jmederos/esp32-r50-kbus/hardware/images/IMG_3665.JPG

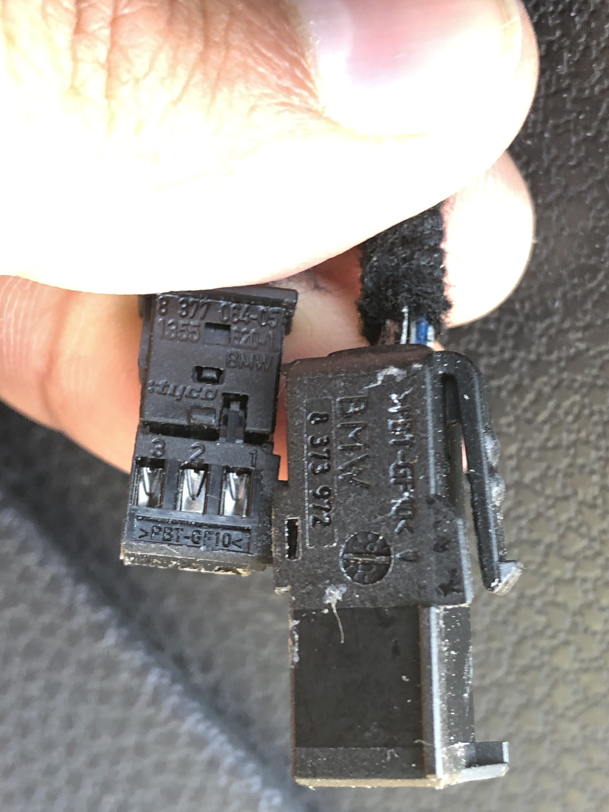
hardware/images/IMG_3665.JPG
