jmederos/esp32-r50-kbus/hardware/images/IMG_3666.JPG

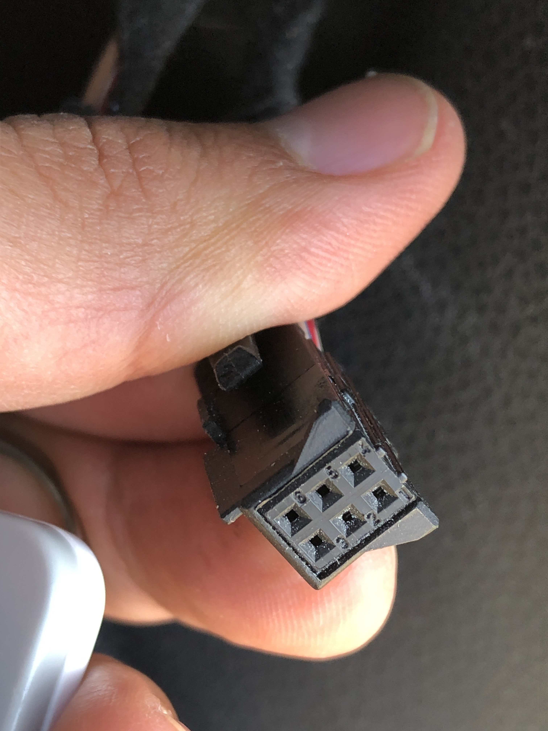
hardware/images/IMG_3666.JPG
