jmederos/esp32-r50-kbus/hardware/images/IMG_4055.JPG

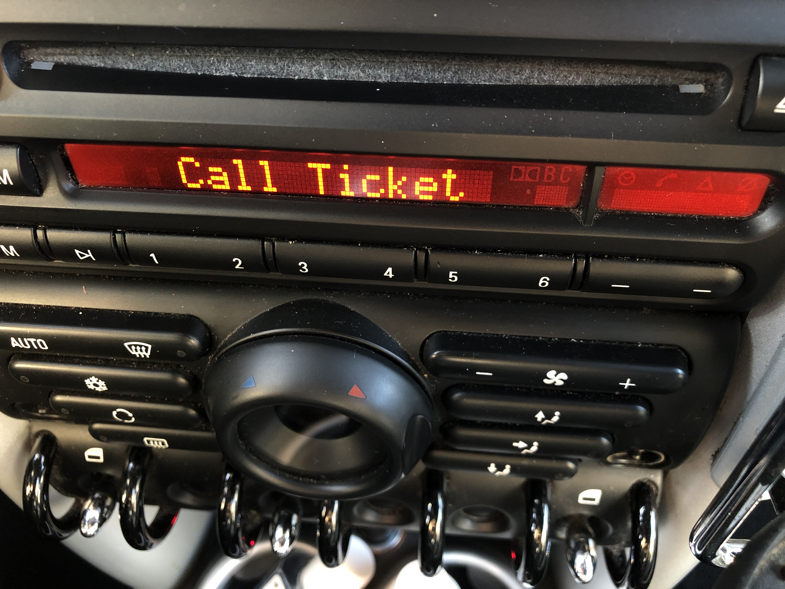
hardware/images/IMG_4055.JPG
