jmederos/esp32-r50-kbus/hardware/images/IMG_4072.JPG

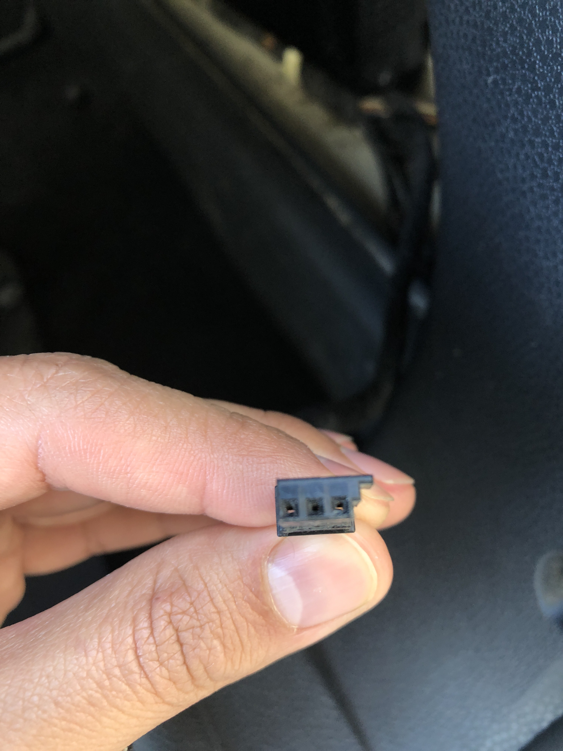
hardware/images/IMG_4072.JPG
