jmederos/esp32-r50-kbus/hardware/images/IMG_4253.JPG

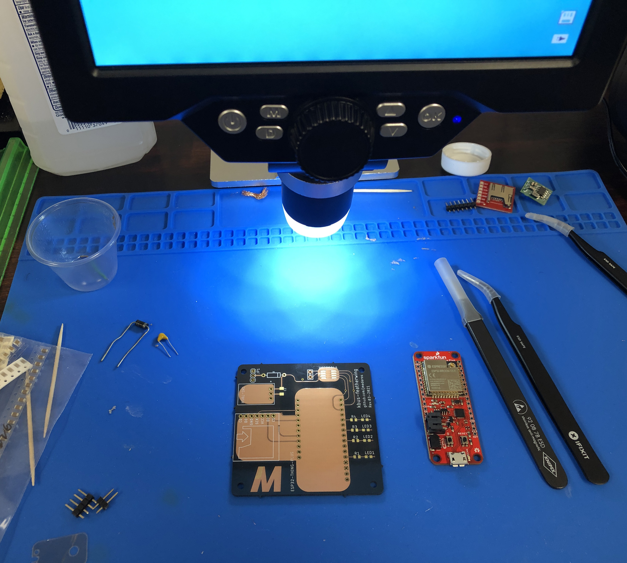
hardware/images/IMG_4253.JPG
